TrendBit/SMBR-hardware/motor_shield_airpump/images/bottom.png

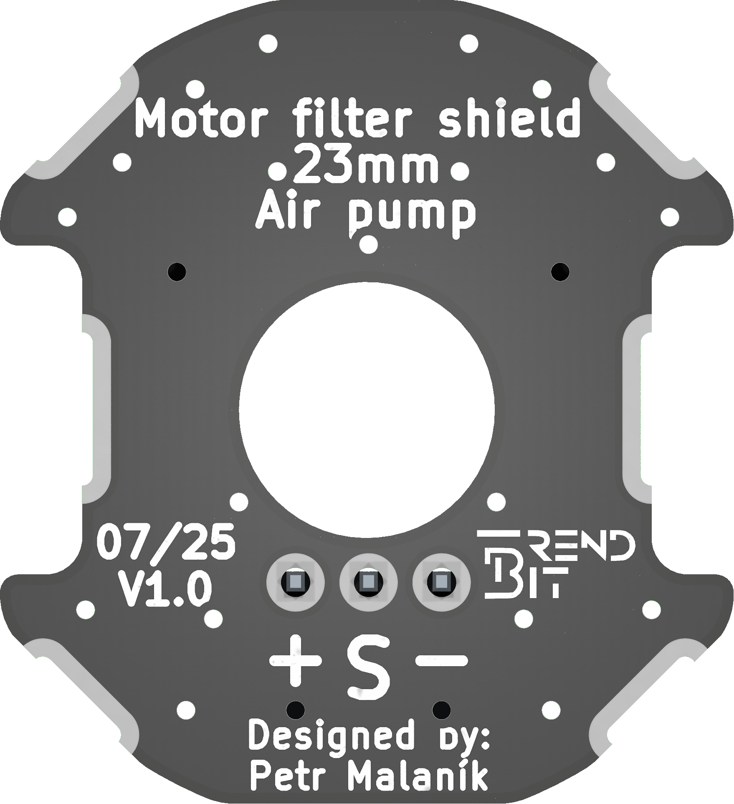
motor_shield_airpump/images/bottom.png
