TrendBit/SMBR-hardware/motor_shield_airpump/images/top.png

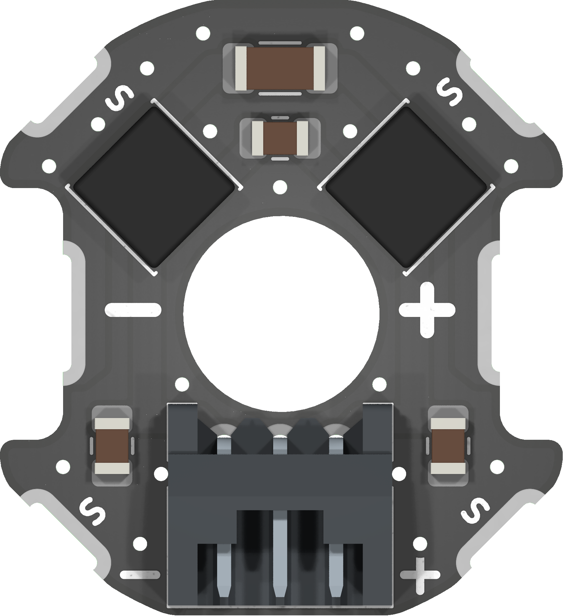
motor_shield_airpump/images/top.png
