TrendBit/SMBR-hardware/pump_board/images/bottom.png

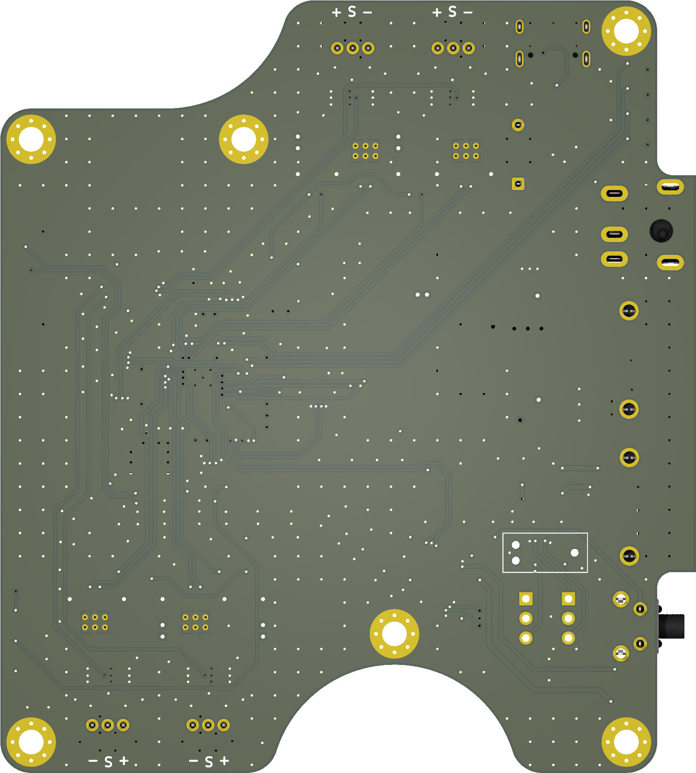
pump_board/images/bottom.png
