TrendBit/SMBR-hardware/resources/hot-surface-warning.png

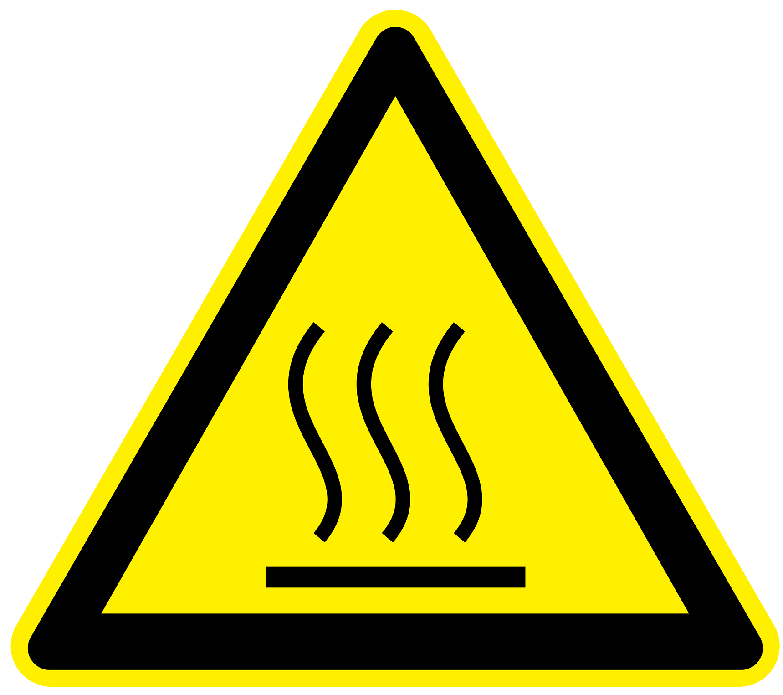
resources/hot-surface-warning.png
