TrendBit/SMBR-hardware/resources/thermometer-sign.png

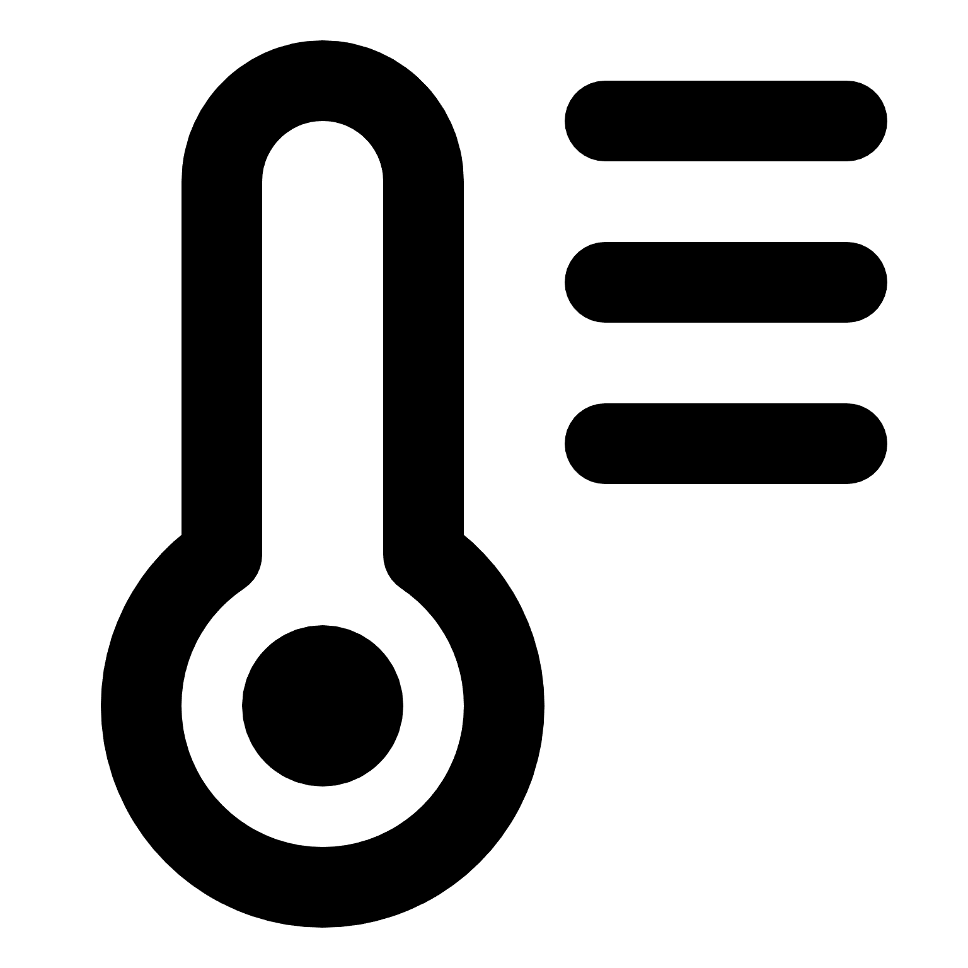
resources/thermometer-sign.png
